tinyboxxx/TiBoard/0. PCB - KiCAD/Tiboard/Tiboard.kicad_sch

## KiCad design 0. PCB - KiCAD/Tiboard/Tiboard.kicad_sch (2022-10-12)

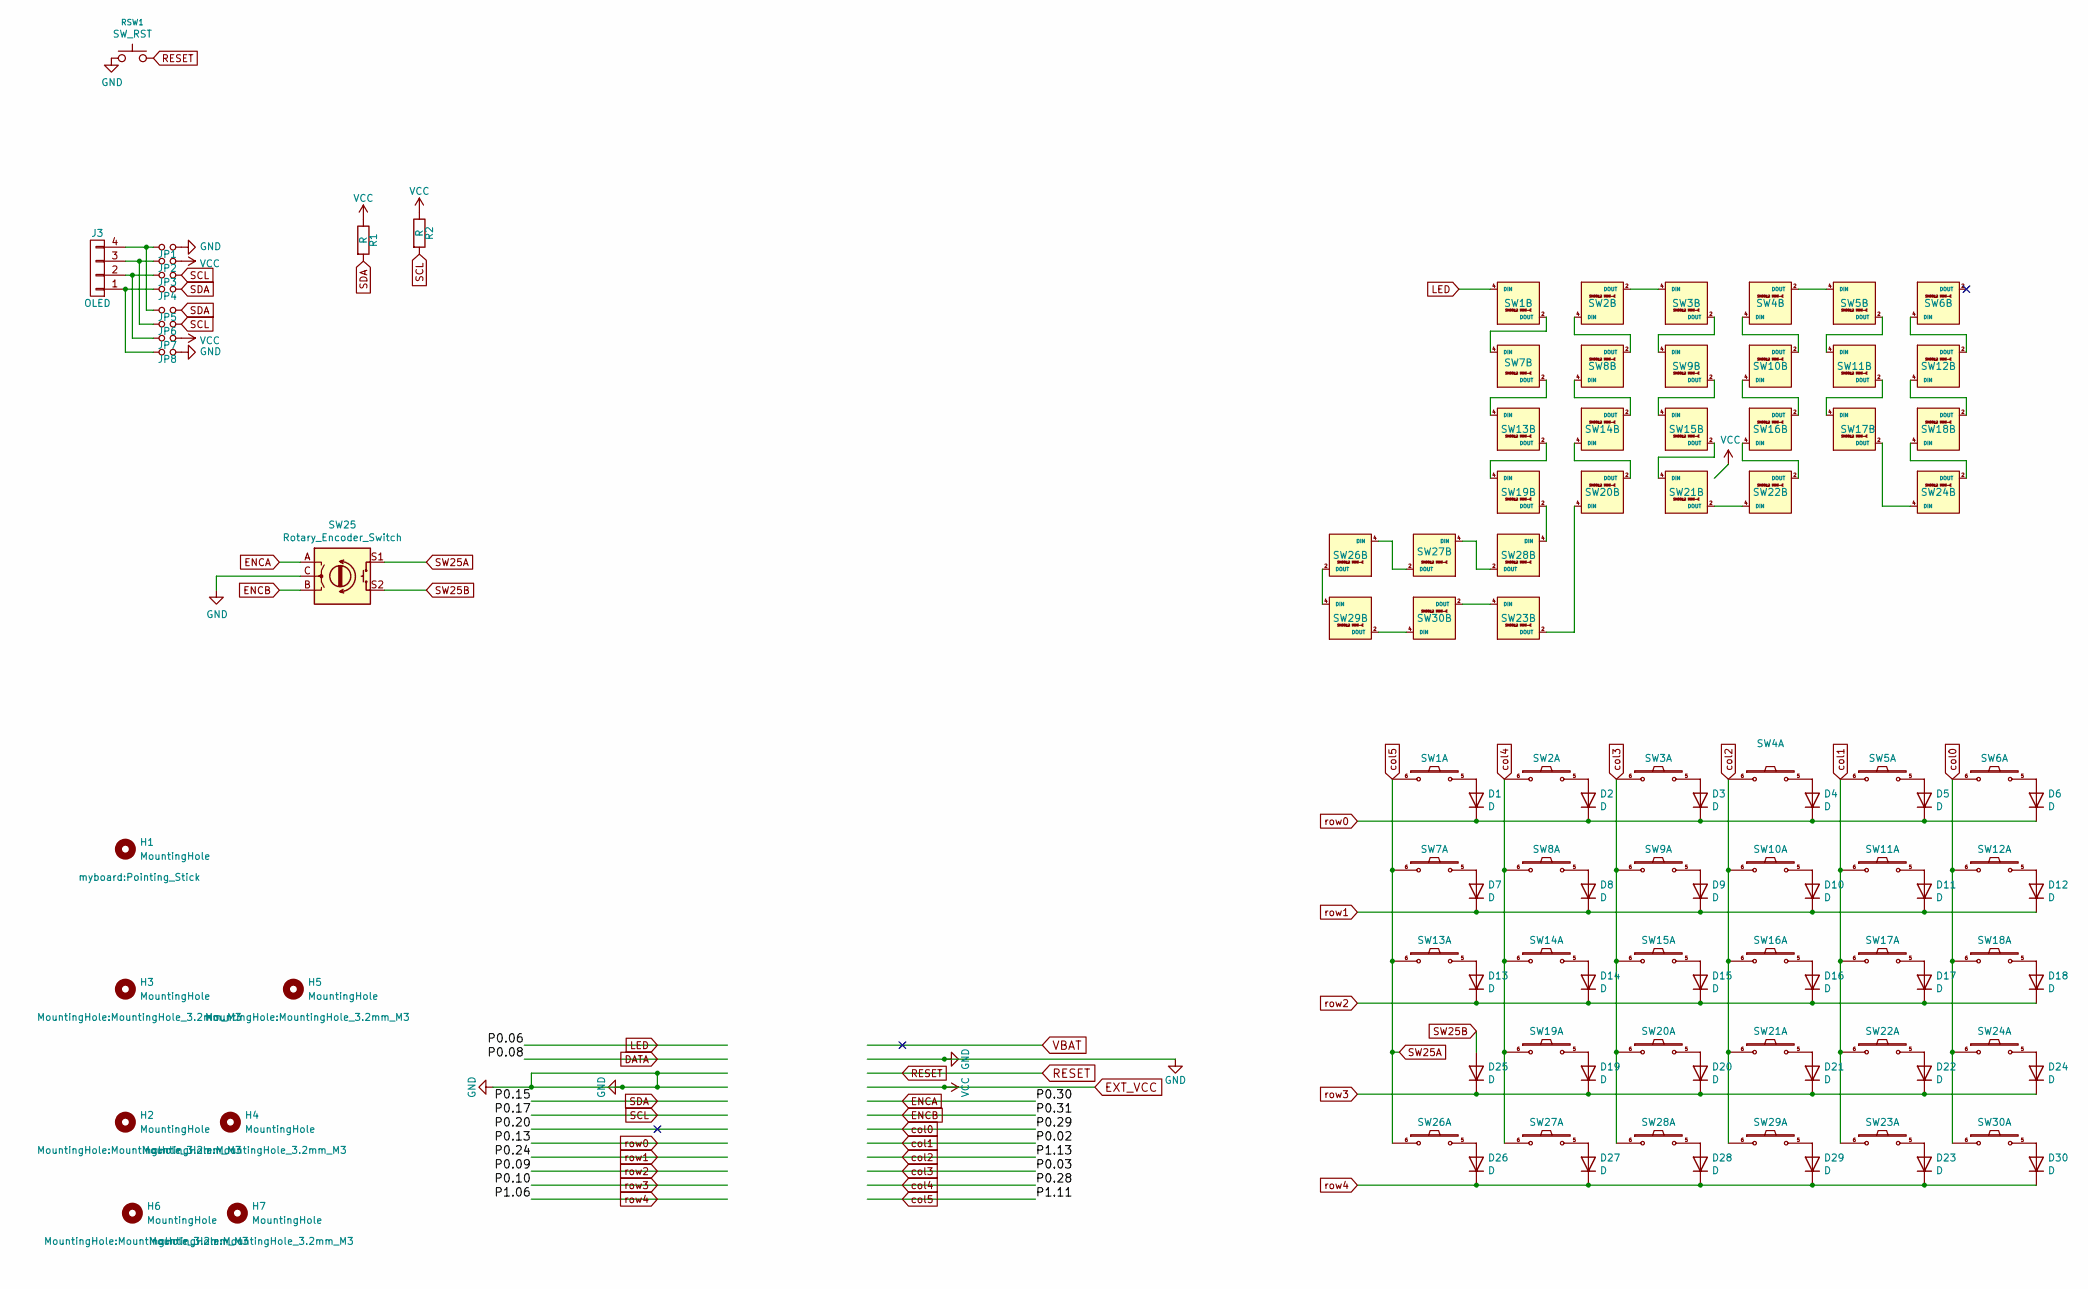
[picture p8: schematic Tiboard.kicad_sch, part in row 1, column 1]

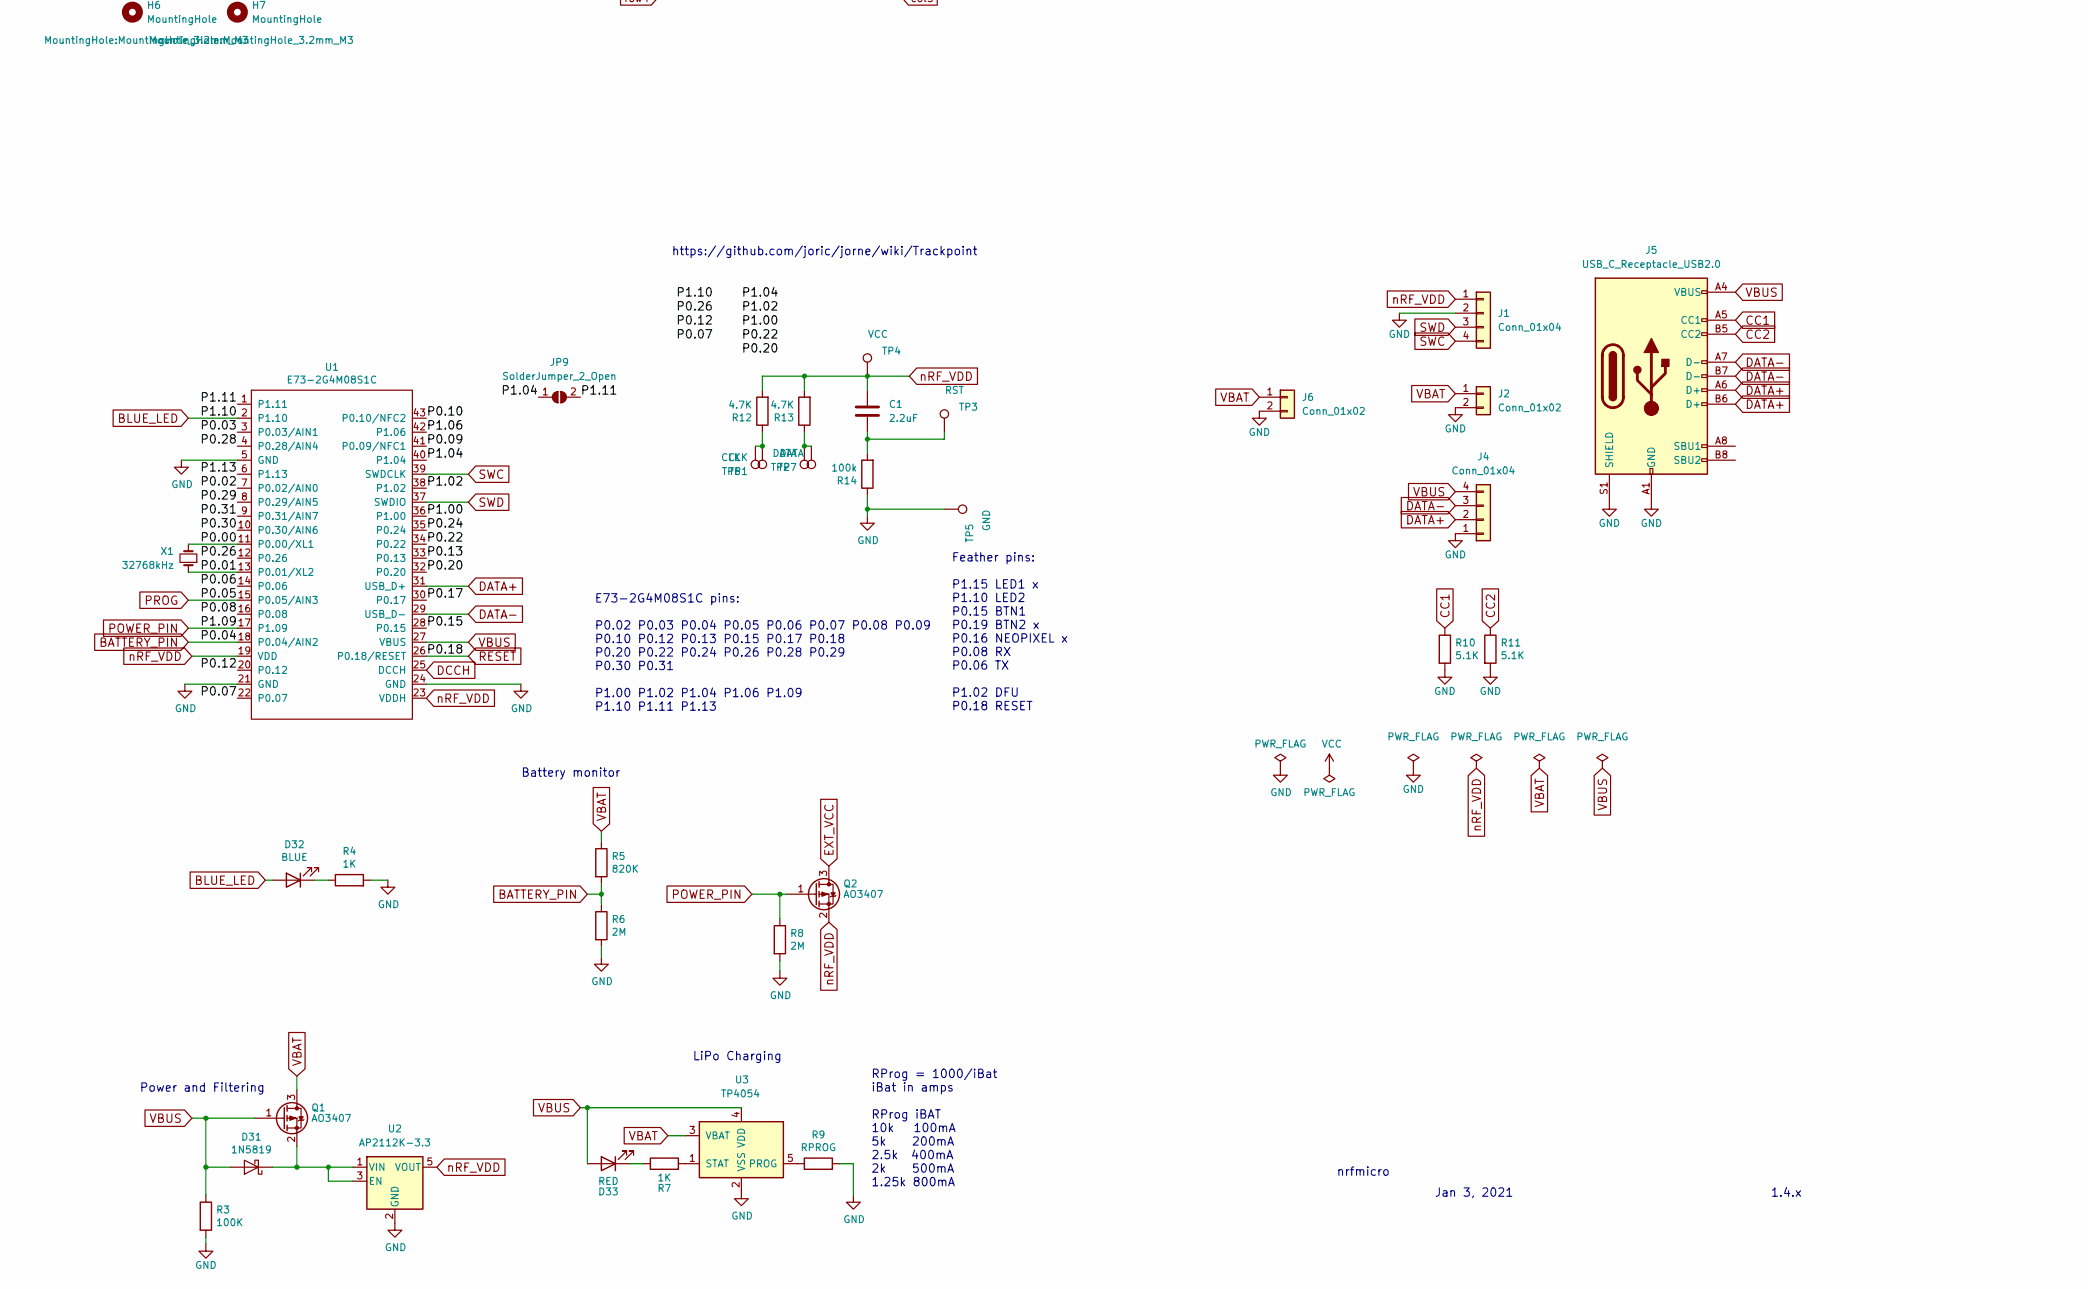
[picture p9: schematic Tiboard.kicad_sch, part in row 2, column 1]

Parts:
C1: 2.2uF; C_0603_1608Metric
D1, D2, D3, D4, D5, D6, D7, D8, D9, D10, D11, D12, D13, D14, D15, D16, D17, D18, D19, D20, D21, D22, D23, D24, D25, D26, D27, D28, D29, D30: D; crkbd-diode-wz-via
D31: 1N5819; D_SOD-323F
D32: BLUE; LED_0603_1608Metric
D33: RED; LED_0603_1608Metric
H1: MountingHole; Pointing_Stick
H2, H3, H4, H5, H6, H7: MountingHole; MountingHole_3.2mm_M3
J1: Conn_01x04; connector_swd
J2: Conn_01x02; connector_bat
J3: OLED; OLED_4Pin
J4: Conn_01x04; connector_usb
J5: USB_C_Receptacle_USB2.0; USB_C_Receptacle_HRO_TYPE-C-31-M-12
J6: Conn_01x02; PinSocket_1x02_P2.54mm_Vertical
JP1, JP2, JP3, JP4, JP5, JP6, JP7, JP8: Jumper_NO_Small; Jumper
JP9: SolderJumper_2_Open; Jumper_SMD
Q1, Q2: AO3407; SOT-23
R1, R2: R; R_0603_1608Metric
R3: 100K; R_0603_1608Metric
R4, R7: 1K; R_0603_1608Metric
R5: 820K; R_0603_1608Metric
R6, R8: 2M; R_0603_1608Metric
R9: RPROG; R_0603_1608Metric
R10, R11: 5.1K; R_0603_1608Metric
R12, R13: 4.7K; R_0603_1608Metric
R14: 100k; R_0603_1608Metric
RSW1: SW_RST; SW_SPST_CK_KXT3
SW1, SW2, SW3, SW4, SW5, SW6, SW7, SW8, SW9, SW10, SW11, SW12, SW13, SW14, SW15, SW16, SW17, SW18, SW19, SW20, SW21, SW22, SW23, SW24, SW26, SW27, SW28, SW29, SW30: SW_PUSH_LED; Choc_Hotswap_SK6812MiniE_trace
SW25: Rotary_Encoder_Switch; RotaryEncoder_Alps_EC11E-Switch_Vertical_H20mm-keebio_modif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
TP1, TP6: CLK; TestPoint_Pad_1.0x1.0mm
TP2, TP7: DATA; TestPoint_Pad_1.0x1.0mm
TP3: RST; TestPoint_Pad_1.0x1.0mm
TP4: VCC; TestPoint_Pad_1.0x1.0mm
TP5: GND; TestPoint_Pad_1.0x1.0mm
U1: E73-2G4M08S1C; E73-2G4M08S1C-52840
U2: AP2112K-3.3; SOT-23-5
U3: TP4054; SOT-23-5
X1: 32768kHz; Crystal_SMD_MicroCrystal_CM9V-T1A-2Pin_1.6x1.0mm

Connections:
BATTERY_PIN: R5.2, R6.1, U1.18 (P0.04/AIN2)
BLUE_LED: D32.2 (A), U1.2 (P1.10)
CC1: J5.A5 (CC1), R10.1
CC2: J5.B5 (CC2), R11.1
DATA: U1.16 (P0.08)
DATA+: J4.2, J5.A6 (D+), J5.B6 (D+), U1.31 (USB_D+)
DATA-: J4.3, J5.A7 (D-), J5.B7 (D-), U1.29 (USB_D-)
DCCH: U1.25 (DCCH)
ENCA: SW25.A, U1.10 (P0.30/AIN6)
ENCB: SW25.B, U1.9 (P0.31/AIN7)
EXT_VCC: JP2.2, JP7.2, Q2.3 (D), R1.1, R2.1, SW21.1 (VDD)
GND: J1.2, J2.2, J4.1, J5.A1 (GND), J5.A12 (GND), J5.B1 (GND), J5.B12 (GND), J5.S1 (SHIELD), J6.2, JP1.2, JP8.2, R3.2, R4.2, R6.2, R8.2, R9.2, R10.2, R11.2, R14.1, RSW1.1, SW25.C, TP5.1, U1.5 (GND), U1.21 (GND), U1.24 (GND), U2.2 (GND), U3.2 (VSS)
LED: SW1.4 (DIN), U1.14 (P0.06)
unnamed: C1.2, R14.2, TP3.1
unnamed: D1.2 (A), SW1.5
unnamed: D2.2 (A), SW2.5
unnamed: D3.2 (A), SW3.5
unnamed: D4.2 (A), SW4.5
unnamed: D5.2 (A), SW5.5
unnamed: D6.2 (A), SW6.5
unnamed: D7.2 (A), SW7.5
unnamed: D8.2 (A), SW8.5
unnamed: D9.2 (A), SW9.5
unnamed: D10.2 (A), SW10.5
unnamed: D11.2 (A), SW11.5
unnamed: D12.2 (A), SW12.5
unnamed: D13.2 (A), SW13.5
unnamed: D14.2 (A), SW14.5
unnamed: D15.2 (A), SW15.5
unnamed: D16.2 (A), SW16.5
unnamed: D17.2 (A), SW17.5
unnamed: D18.2 (A), SW18.5
unnamed: D19.2 (A), SW19.5
unnamed: D20.2 (A), SW20.5
unnamed: D21.2 (A), SW21.5
unnamed: D22.2 (A), SW22.5
unnamed: D23.2 (A), SW23.5
unnamed: D24.2 (A), SW24.5
unnamed: D26.2 (A), SW26.5
unnamed: D27.2 (A), SW27.5
unnamed: D28.2 (A), SW28.5
unnamed: D29.2 (A), SW29.5
unnamed: D30.2 (A), SW30.5
unnamed: D31.1 (K), Q1.2 (S), U2.1 (VIN), U2.3 (EN)
unnamed: D32.1 (K), R4.1
unnamed: D33.1 (K), R7.1
unnamed: J3.1, JP4.1, JP8.1
unnamed: J3.2, JP3.1, JP7.1
unnamed: J3.3, JP2.1, JP6.1
unnamed: J3.4, JP1.1, JP5.1
unnamed: R7.2, U3.1 (STAT)
unnamed: R9.1, U3.5 (PROG)
unnamed: R12.1, TP1.1, TP6.1
unnamed: R13.1, TP2.1, TP7.1
unnamed: SW1.2 (DOUT), SW7.4 (DIN)
unnamed: SW2.2 (DOUT), SW3.4 (DIN)
unnamed: SW2.4 (DIN), SW8.2 (DOUT)
unnamed: SW3.2 (DOUT), SW9.4 (DIN)
unnamed: SW4.2 (DOUT), SW5.4 (DIN)
unnamed: SW4.4 (DIN), SW10.2 (DOUT)
unnamed: SW10.4 (DIN), SW16.2 (DOUT)
unnamed: SW11.2 (DOUT), SW17.4 (DIN)
unnamed: SW5.2 (DOUT), SW11.4 (DIN)
unnamed: SW6.4 (DIN), SW12.2 (DOUT)
unnamed: SW12.4 (DIN), SW18.2 (DOUT)
unnamed: SW13.2 (DOUT), SW19.4 (DIN)
unnamed: SW7.2 (DOUT), SW13.4 (DIN)
unnamed: SW8.4 (DIN), SW14.2 (DOUT)
unnamed: SW14.4 (DIN), SW20.2 (DOUT)
unnamed: SW15.2 (DOUT), SW21.4 (DIN)
unnamed: SW9.2 (DOUT), SW15.4 (DIN)
unnamed: SW16.4 (DIN), SW22.2 (DOUT)
unnamed: SW17.2 (DOUT), SW24.4 (DIN)
unnamed: SW18.4 (DIN), SW24.2 (DOUT)
unnamed: SW19.2 (DOUT), SW28.4 (DIN)
unnamed: SW20.4 (DIN), SW23.2 (DOUT)
unnamed: SW21.2 (DOUT), SW22.4 (DIN)
unnamed: SW23.4 (DIN), SW30.2 (DOUT)
unnamed: SW26.2 (DOUT), SW29.4 (DIN)
unnamed: SW26.4 (DIN), SW27.2 (DOUT)
unnamed: SW27.4 (DIN), SW28.2 (DOUT)
unnamed: SW29.2 (DOUT), SW30.4 (DIN)
P0.00: U1.11 (P0.00/XL1), X1.2
P0.01: U1.13 (P0.01/XL2), X1.1
P0.07: U1.22 (P0.07)
P0.12: U1.20 (P0.12)
P0.20: U1.32 (P0.20)
P0.22: U1.34 (P0.22)
P0.26: U1.12 (P0.26)
P1.00: U1.36 (P1.00)
P1.02: U1.38 (P1.02)
P1.04: JP9.1 (A), U1.40 (P1.04)
POWER_PIN: Q2.1 (G), R8.1, U1.17 (P1.09)
PROG: U1.15 (P0.05/AIN3)
RESET: RSW1.2, U1.26 (P0.18/RESET)
SCL: JP3.2, JP6.2, R2.2, U1.30 (P0.17)
SDA: JP4.2, JP5.2, R1.2, U1.28 (P0.15)
SW25B: D25.2 (A), SW25.S2
SWC: J1.4, U1.39 (SWDCLK)
SWD: J1.3, U1.37 (SWDIO)
VBAT: J2.1, J6.1, Q1.3 (D), R5.1, U3.3 (VBAT)
VBUS: D31.2 (A), D33.2 (A), J4.4, J5.A4 (VBUS), J5.A9 (VBUS), J5.B4 (VBUS), J5.B9 (VBUS), Q1.1 (G), R3.1, U1.27 (VBUS), U3.4 (VDD)
col0: SW6.6, SW12.6, SW18.6, SW24.6, SW30.6, U1.8 (P0.29/AIN5)
col1: SW5.6, SW11.6, SW17.6, SW22.6, SW23.6, U1.7 (P0.02/AIN0)
col2: SW4.6, SW10.6, SW16.6, SW21.6, SW29.6, U1.6 (P1.13)
col3: SW3.6, SW9.6, SW15.6, SW20.6, SW28.6, U1.3 (P0.03/AIN1)
col4: SW2.6, SW8.6, SW14.6, SW19.6, SW27.6, U1.4 (P0.28/AIN4)
col5: JP9.2 (B), SW1.6, SW7.6, SW13.6, SW25.S1, SW26.6, U1.1 (P1.11)
nRF_VDD: C1.1, J1.1, Q2.2 (S), R12.2, R13.2, TP4.1, U1.19 (VDD), U1.23 (VDDH), U2.5 (VOUT)
row0: D1.1 (K), D2.1 (K), D3.1 (K), D4.1 (K), D5.1 (K), D6.1 (K), U1.33 (P0.13)
row1: D7.1 (K), D8.1 (K), D9.1 (K), D10.1 (K), D11.1 (K), D12.1 (K), U1.35 (P0.24)
row2: D13.1 (K), D14.1 (K), D15.1 (K), D16.1 (K), D17.1 (K), D18.1 (K), U1.41 (P0.09/NFC1)
row3: D19.1 (K), D20.1 (K), D21.1 (K), D22.1 (K), D24.1 (K), D25.1 (K), U1.43 (P0.10/NFC2)
row4: D23.1 (K), D26.1 (K), D27.1 (K), D28.1 (K), D29.1 (K), D30.1 (K), U1.42 (P1.06)

Notes on the sheet:
1.4.x
LiPo Charging
Power and Filtering
Feather pins: P1.15 LED1 x P1.10 LED2 P0.15 BTN1 P0.19 BTN2 x P0.16 NEOPIXEL x P0.08 RX P0.06 TX P1.02 DFU P0.18 RESET
RProg = 1000/iBat iBat in amps RProg iBAT 10k 100mA 5k 200mA 2.5k 400mA 2k 500mA 1.25k 800mA
https://github.com/joric/jorne/wiki/Trackpoint
Battery monitor
nrfmicro
E73-2G4M08S1C pins: P0.02 P0.03 P0.04 P0.05 P0.06 P0.07 P0.08 P0.09 P0.10 P0.12 P0.13 P0.15 P0.17 P0.18 P0.20 P0.22 P0.24 P0.26 P0.28 P0.29 P0.30 P0.31 P1.00 P1.02 P1.04 P1.06 P1.09 P1.10 P1.11 P1.13
Jan 3, 2021
